serarandal/TFG/DOCUMENTATION/amazon-api-gateway.png

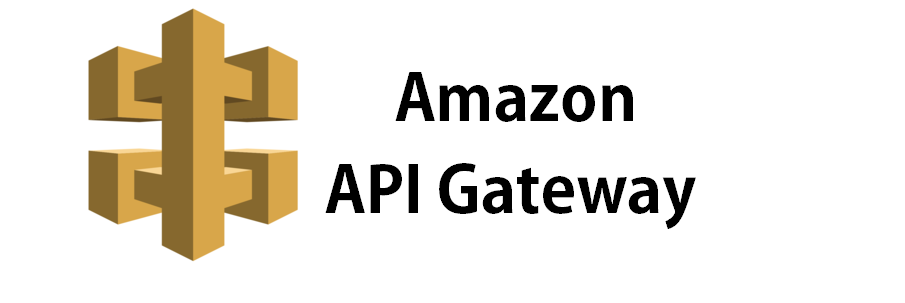
DOCUMENTATION/amazon-api-gateway.png
