serarandal/TFG/DOCUMENTATION/AndroidStudio.png

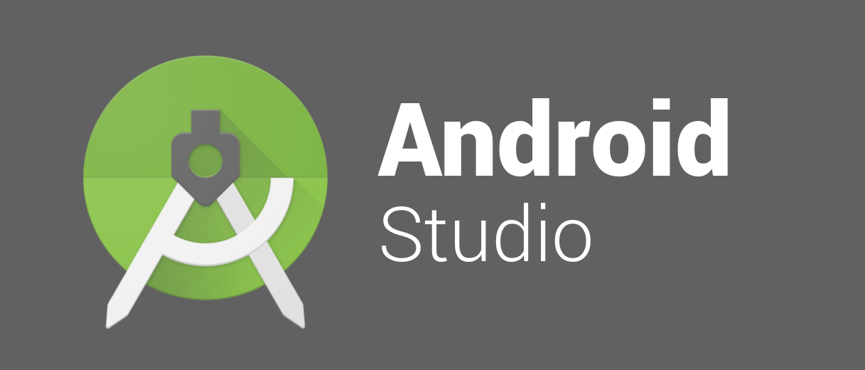
DOCUMENTATION/AndroidStudio.png
