serarandal/TFG/DOCUMENTATION/apimagen.jpg

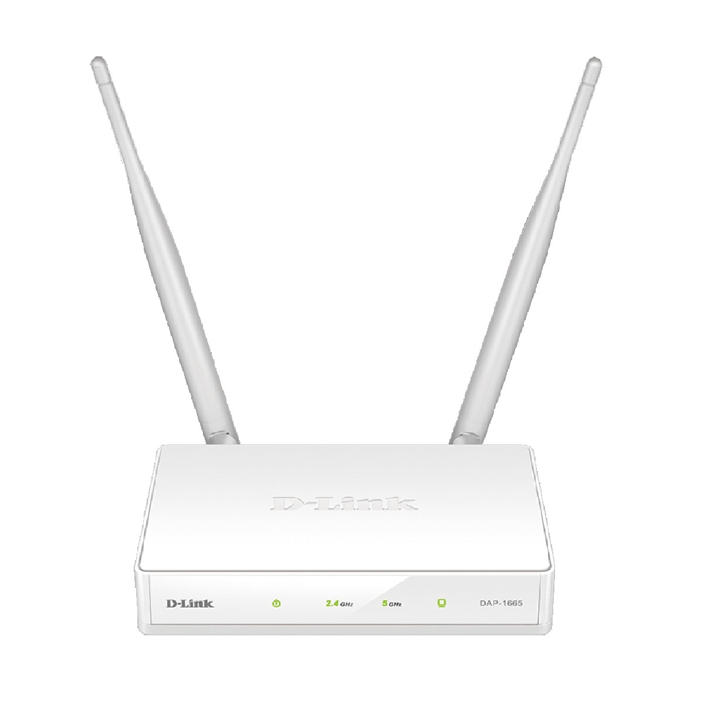
DOCUMENTATION/apimagen.jpg
