serarandal/TFG/DOCUMENTATION/CameraHW.jpg

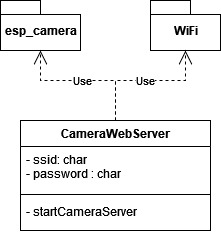
DOCUMENTATION/CameraHW.jpg
