serarandal/TFG/DOCUMENTATION/CapturaAndroidAPPControl.PNG

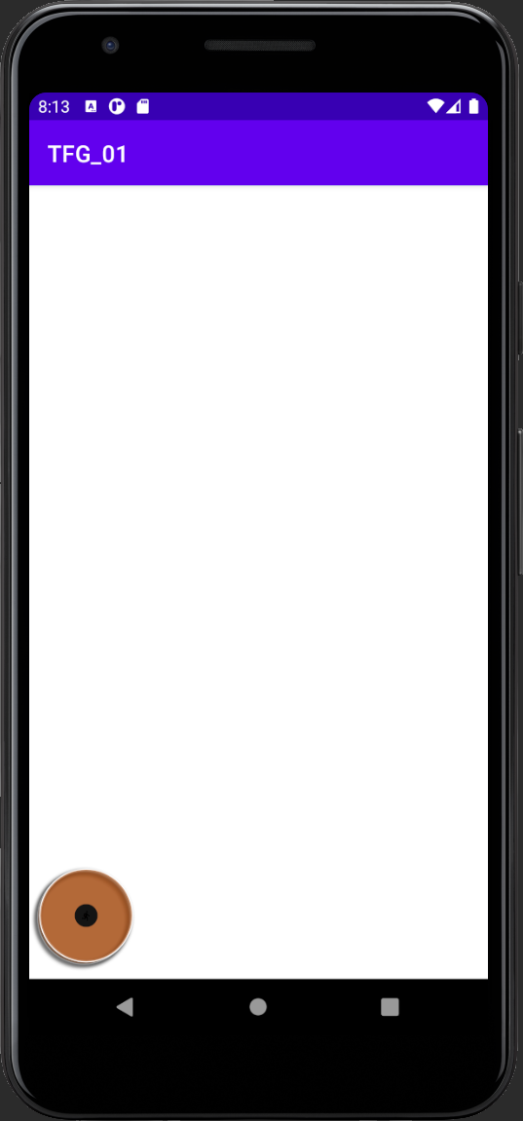
DOCUMENTATION/CapturaAndroidAPPControl.PNG
