serarandal/TFG/DOCUMENTATION/CapturaCONTROLAndroidAPP.PNG

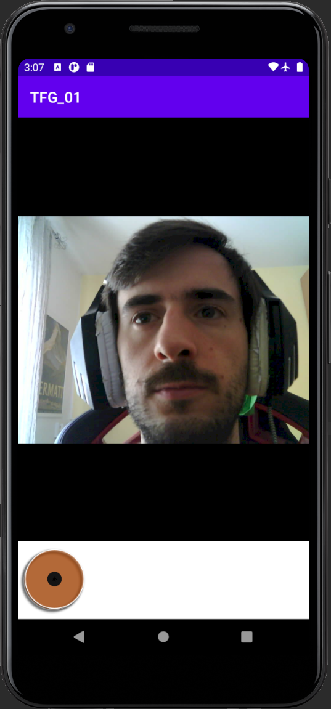
DOCUMENTATION/CapturaCONTROLAndroidAPP.PNG
