serarandal/TFG/DOCUMENTATION/CapturaPCAPP2.PNG

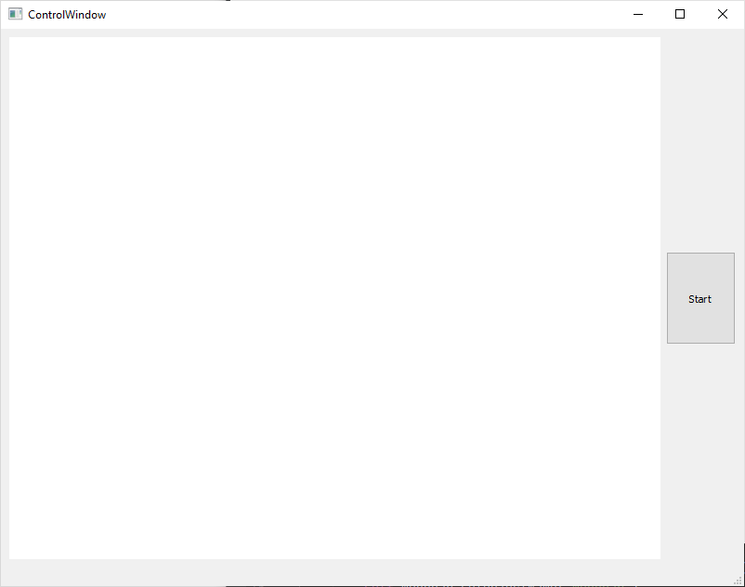
DOCUMENTATION/CapturaPCAPP2.PNG
