serarandal/TFG/DOCUMENTATION/ConfigWindowPC.PNG

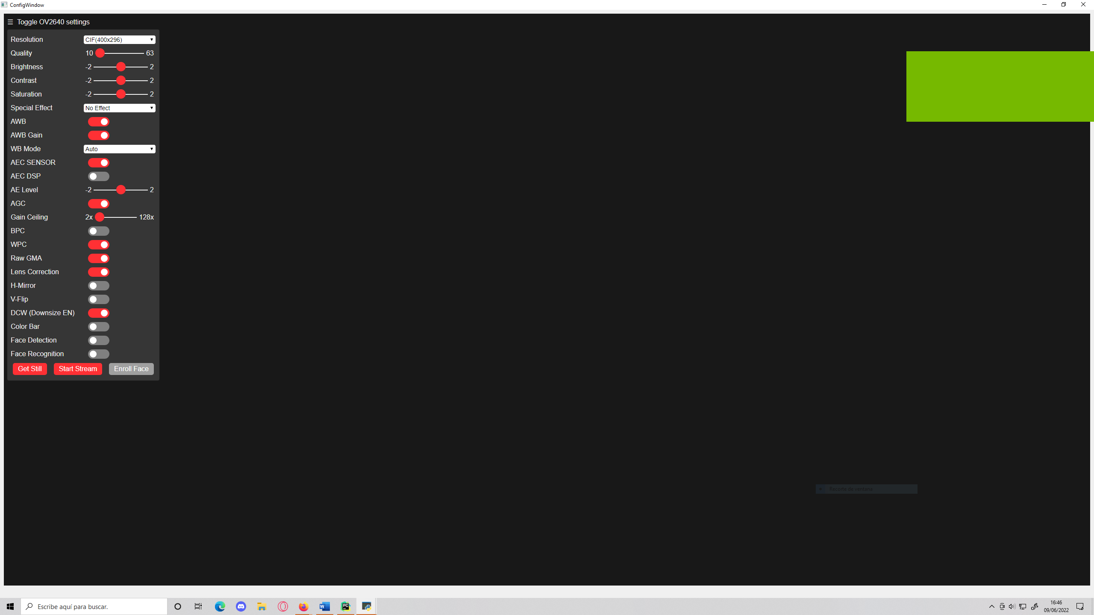
DOCUMENTATION/ConfigWindowPC.PNG
