serarandal/TFG/DOCUMENTATION/Diagrama alto nivel bonito.jpg

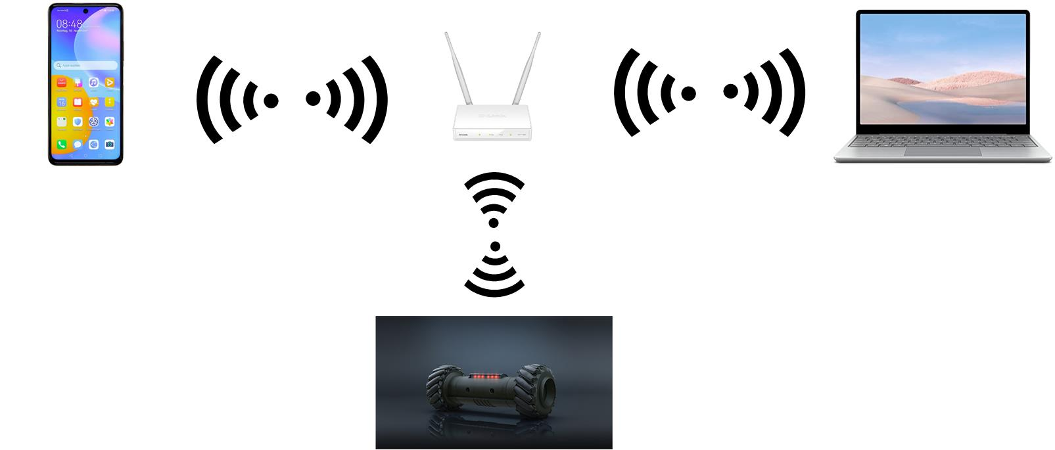
DOCUMENTATION/Diagrama alto nivel bonito.jpg
