serarandal/TFG/DOCUMENTATION/Diagrama de Gantt.jpg

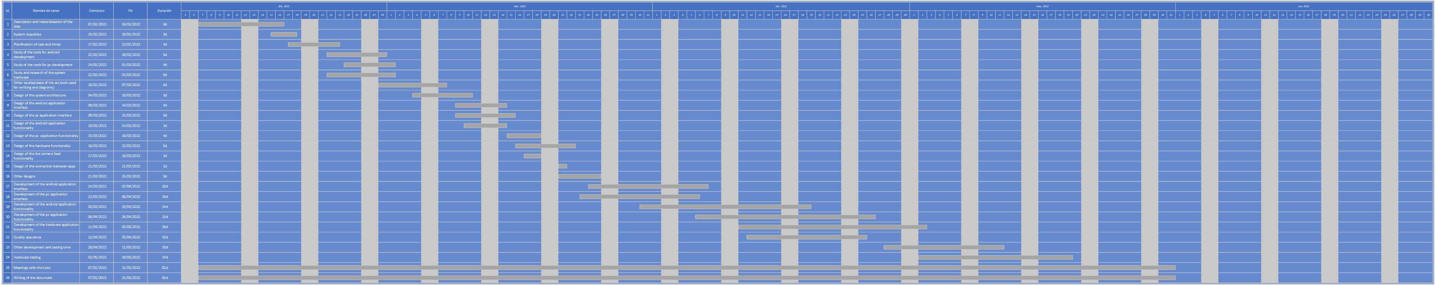
DOCUMENTATION/Diagrama de Gantt.jpg
