serarandal/TFG/DOCUMENTATION/esp32-cam.jpg

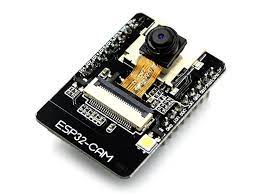
DOCUMENTATION/esp32-cam.jpg
