serarandal/TFG/DOCUMENTATION/Golang.png

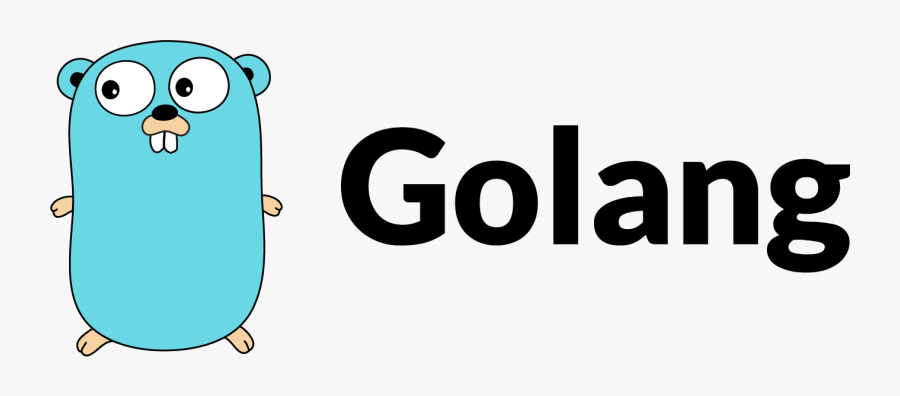
DOCUMENTATION/Golang.png
