serarandal/TFG/DOCUMENTATION/IVZ132203_WeMos-D1-mini-Wifi-Module_x.png

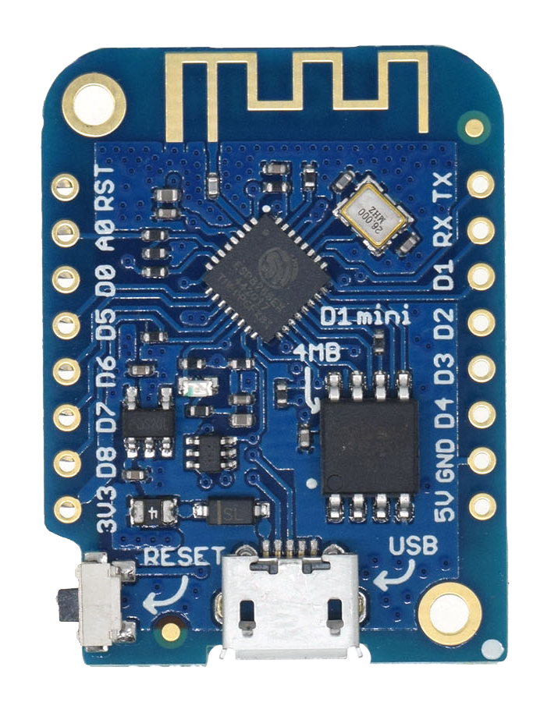
DOCUMENTATION/IVZ132203_WeMos-D1-mini-Wifi-Module_x.png
