serarandal/TFG/DOCUMENTATION/mulesoft.png

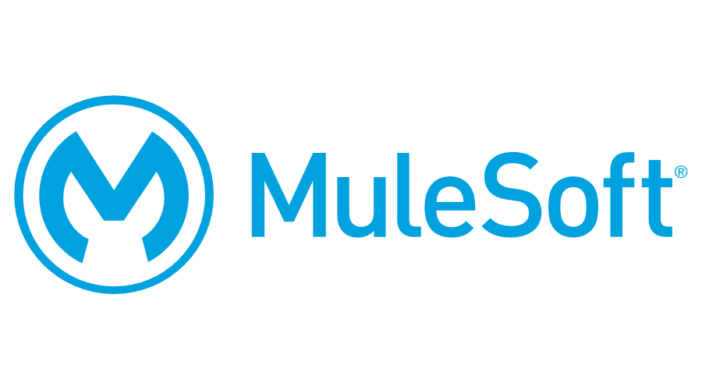
DOCUMENTATION/mulesoft.png
