serarandal/TFG/DOCUMENTATION/portatilimagen.jpg

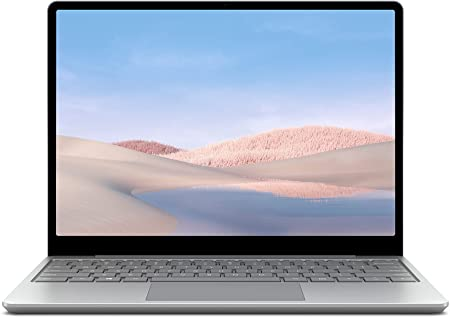
DOCUMENTATION/portatilimagen.jpg
