serarandal/TFG/DOCUMENTATION/Python_and_Qt.png

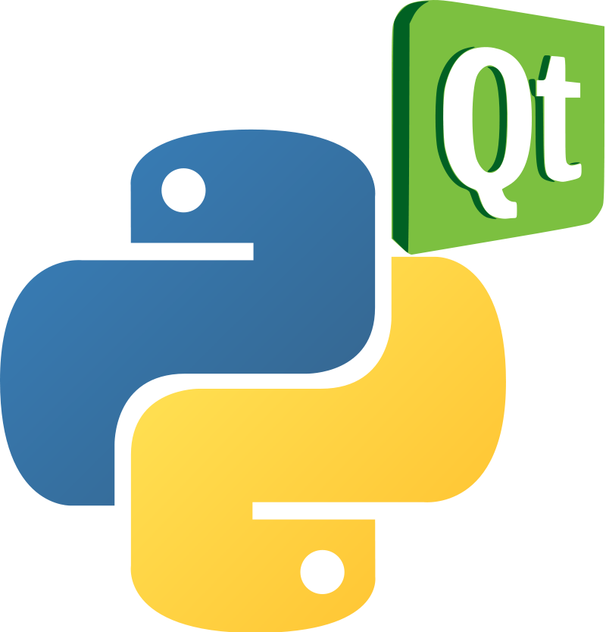
DOCUMENTATION/Python_and_Qt.png
