serarandal/TFG/DOCUMENTATION/subversion.png

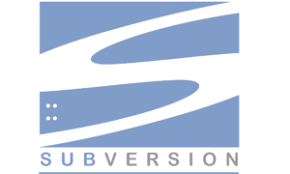
DOCUMENTATION/subversion.png
