serarandal/TFG/DOCUMENTATION/telefonoimagen.jpg

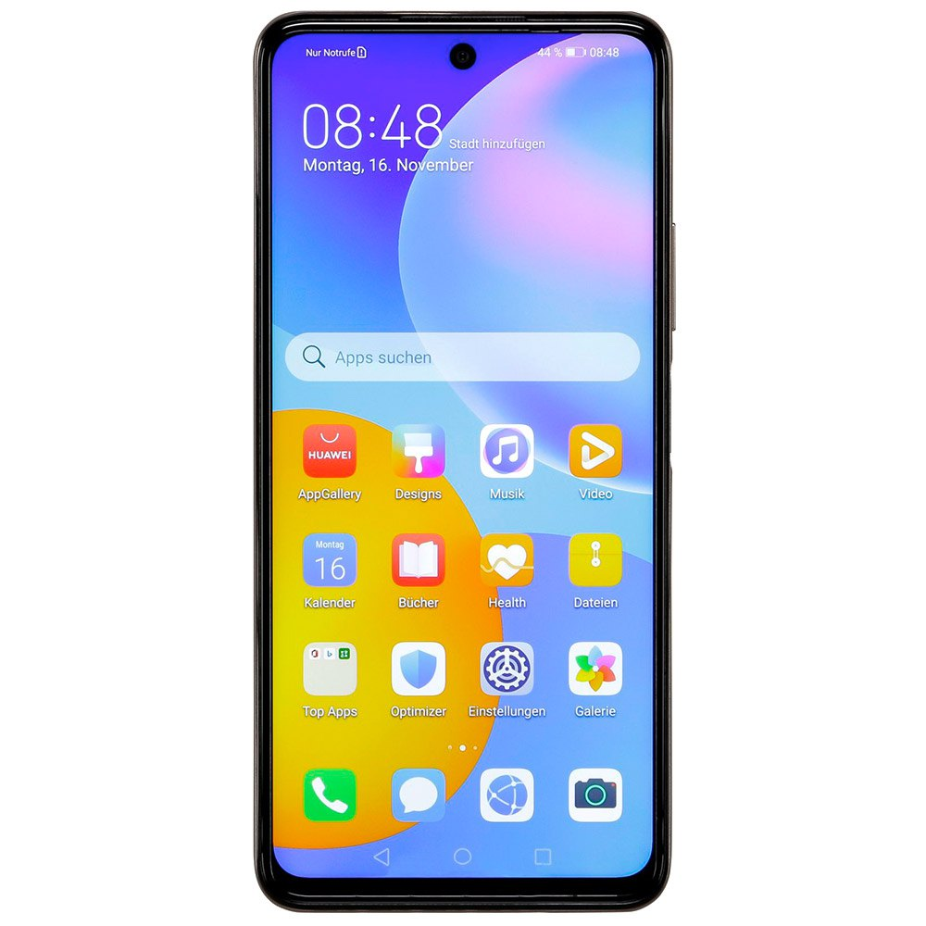
DOCUMENTATION/telefonoimagen.jpg
