serarandal/TFG/TFG_PC_APP/Screenshot from 2022-02-17 10-21-56.png

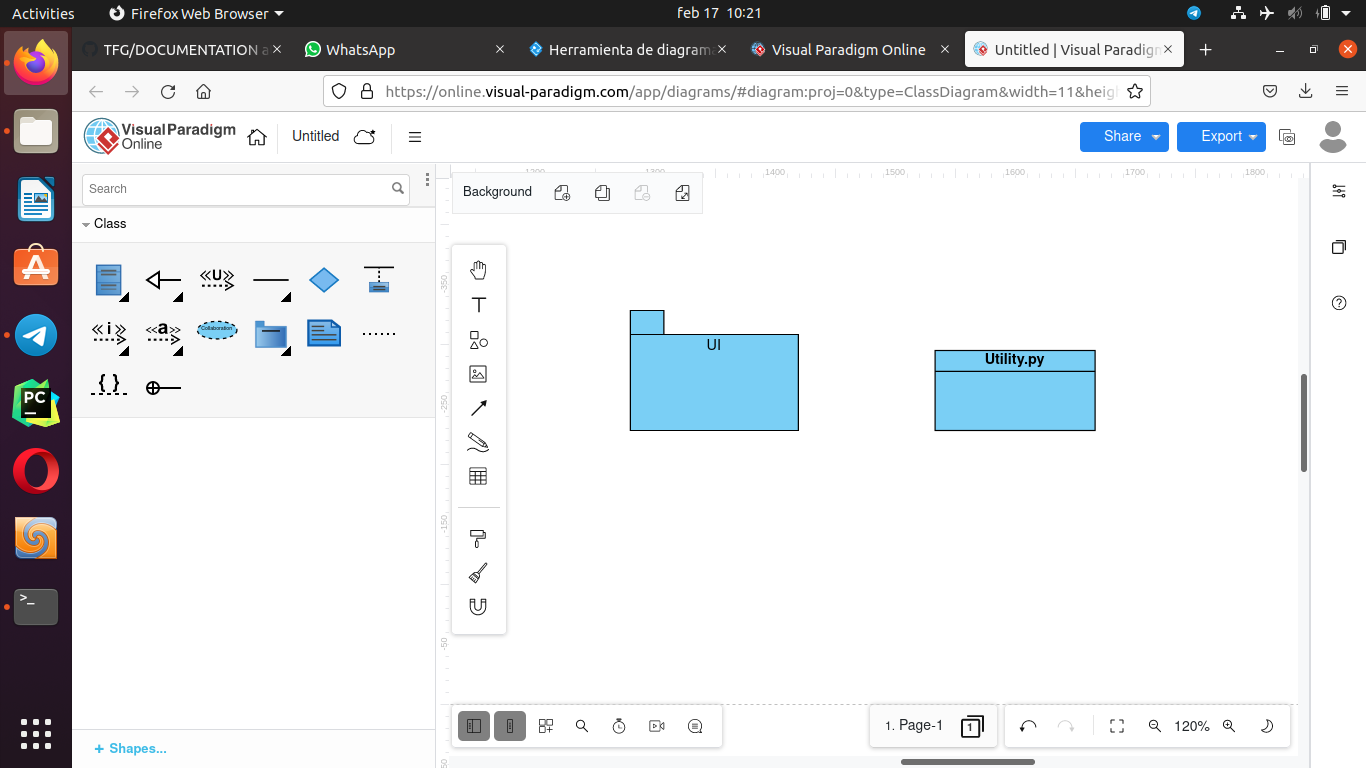
TFG_PC_APP/Screenshot from 2022-02-17 10-21-56.png
