serarandal/TFG/TFG_HWD/12_OTA/config.h

const char* ssid     = "MOVISTAR_D458";
const char* password = "z9YrPTJsyvwtyr4KsC7s";
const char* hostname = "ESP8266_1";

IPAddress ip(192, 168, 1, 200);
IPAddress gateway(192, 168, 1, 1);
IPAddress subnet(255, 255, 255, 0);
